open-headset-interconnect-standard/radio-adapter/GX16-8P-Horizontal/GX16-8P-Horizontal/GX16-8P-Horizontal.kicad_pcb

## KiCad design GX16-8P-Horizontal/GX16-8P-Horizontal/GX16-8P-Horizontal.kicad_pcb (2024-04-24)

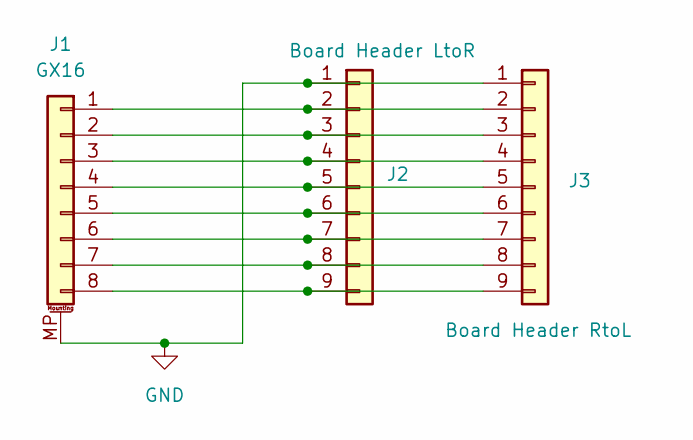
[picture p22: schematic GX16-8P-Horizontal.kicad_sch]

Parts:
J1: GX16; Conn_GX16-8_8pin_Aviation; Part Number GX16-F-8P
J2: Board Header LtoR; Conn_B2B-RA_2.54mm_ThroughPads_9pin_LtoR
J3: Board Header RtoL; Conn_B2B-RA_2.54mm_ThroughPads_9pin_RtoL

Connections:
GND: J1.MP (MountPin), J2.1, J3.1
unnamed: J1.1, J2.2, J3.2
unnamed: J1.2, J2.3, J3.3
unnamed: J1.3, J2.4, J3.4
unnamed: J1.4, J2.5, J3.5
unnamed: J1.5, J2.6, J3.6
unnamed: J1.6, J2.7, J3.7
unnamed: J1.7, J2.8, J3.8
unnamed: J1.8, J2.9, J3.9
