open-headset-interconnect-standard/radio-adapter/GX16-8P-Horizontal/GX16-8P-Horizontal/GX16-8P-Horizontal.kicad_pcb

## KiCad design GX16-8P-Horizontal/GX16-8P-Horizontal/GX16-8P-Horizontal.kicad_pcb (continued)

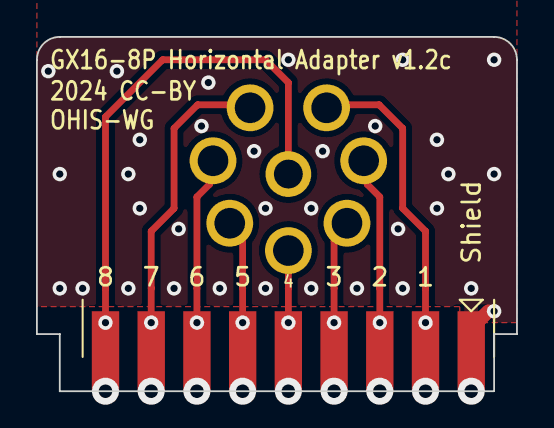
[picture p23: board GX16-8P-Horizontal.kicad_pcb from above]

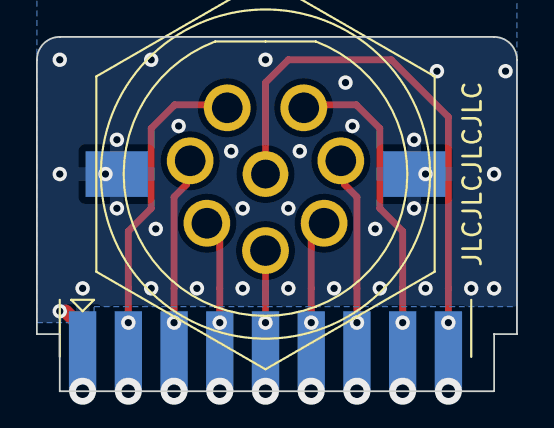
[picture p24: board GX16-8P-Horizontal.kicad_pcb from below]

Board: 2 copper layers, 26.7 x 19.7 mm, 3 parts (2 on the bottom side), 9 nets.
