open-headset-interconnect-standard/radio-adapter/GX16-8P-Horizontal/GX16-8P-Horizontal Slot Test/GX16-8P-Horizontal Slot Test.kicad_pcb

## KiCad design GX16-8P-Horizontal/GX16-8P-Horizontal Slot Test/GX16-8P-Horizontal Slot Test.kicad_pcb (2024-04-24)

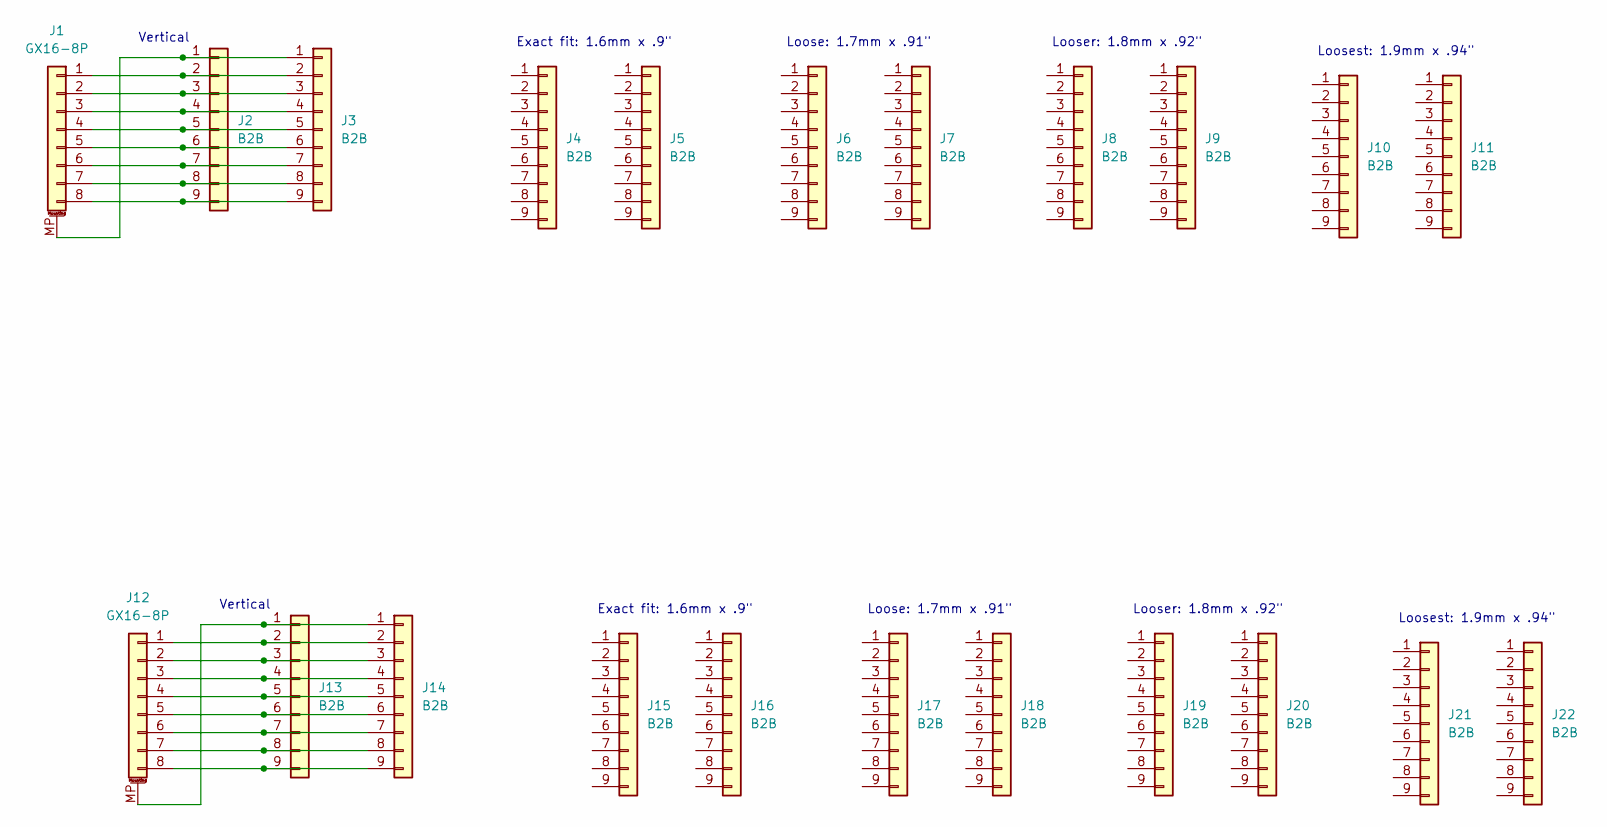
[picture p25: schematic GX16-8P-Horizontal Slot Test.kicad_sch]

Parts:
J1, J12: GX16-8P; Conn_GX16-8_8pin_Aviation
J2, J4, J6, J8, J10, J13, J15, J17, J19, J21: B2B; Conn_B2B-RA_2.54mm_9pin_LtoR
J3, J5, J7, J9, J11, J14, J16, J18, J20, J22: B2B; Conn_B2B-RA_2.54mm_9pin_RtoL

Connections:
unnamed: J1.1, J2.2, J3.2
unnamed: J1.2, J2.3, J3.3
unnamed: J1.3, J2.4, J3.4
unnamed: J1.4, J2.5, J3.5
unnamed: J1.5, J2.6, J3.6
unnamed: J1.6, J2.7, J3.7
unnamed: J1.7, J2.8, J3.8
unnamed: J1.8, J2.9, J3.9
unnamed: J1.MP (MountPin), J2.1, J3.1
unnamed: J12.1, J13.2, J14.2
unnamed: J12.2, J13.3, J14.3
unnamed: J12.3, J13.4, J14.4
unnamed: J12.4, J13.5, J14.5
unnamed: J12.5, J13.6, J14.6
unnamed: J12.6, J13.7, J14.7
unnamed: J12.7, J13.8, J14.8
unnamed: J12.8, J13.9, J14.9
unnamed: J12.MP (MountPin), J13.1, J14.1

Notes on the sheet:
Exact fit: 1.6mm x .9"
Loosest: 1.9mm x .94"
Looser: 1.8mm x .92"
Loose: 1.7mm x .91"
Vertical

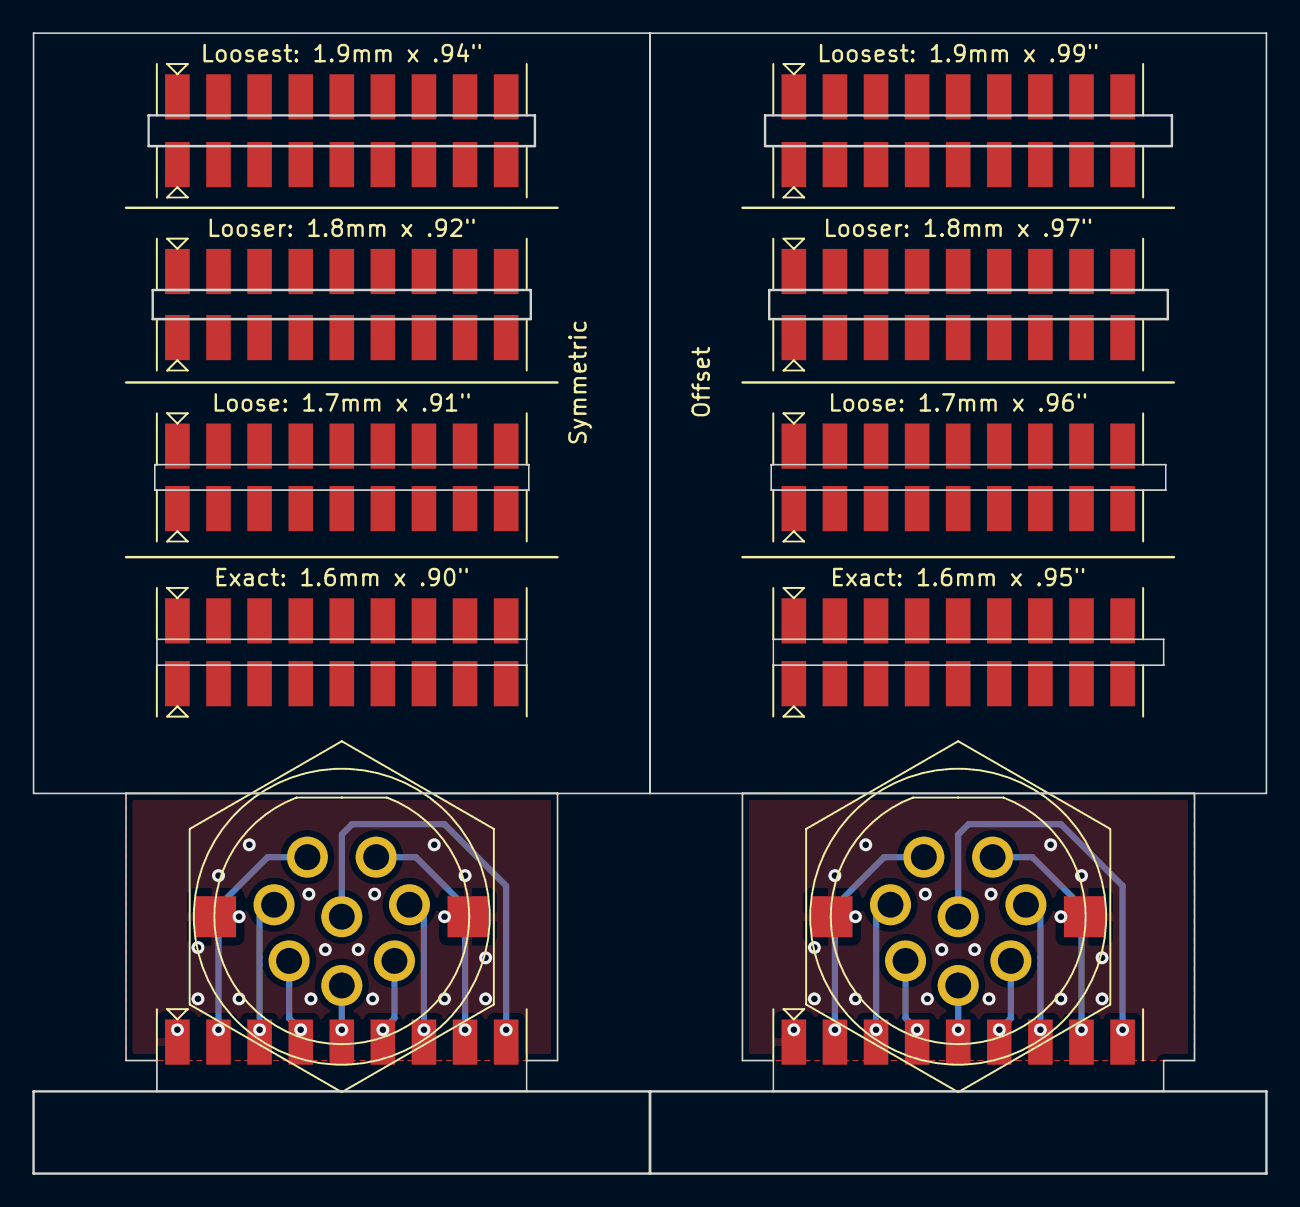
[picture p26: board GX16-8P-Horizontal Slot Test.kicad_pcb from above]

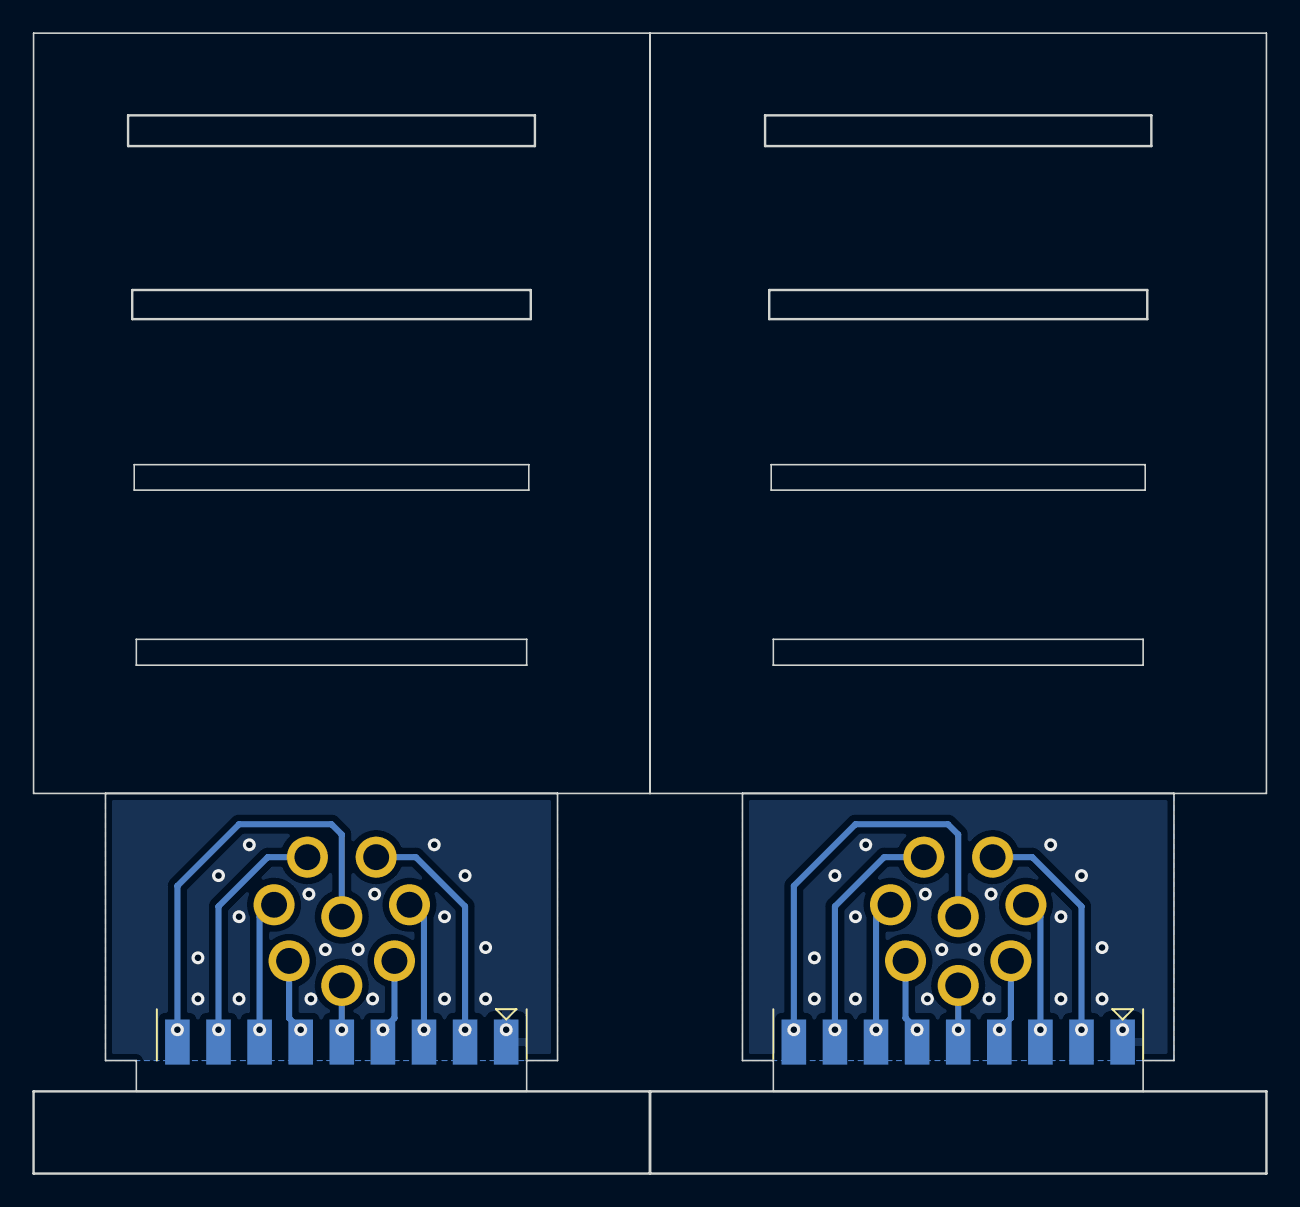
[picture p27: board GX16-8P-Horizontal Slot Test.kicad_pcb from below]

Board: 2 copper layers, 76.2 x 70.5 mm, 22 parts (2 on the bottom side), 18 nets.
